F6ITU/K_Driver/Image/Ajax.bmp

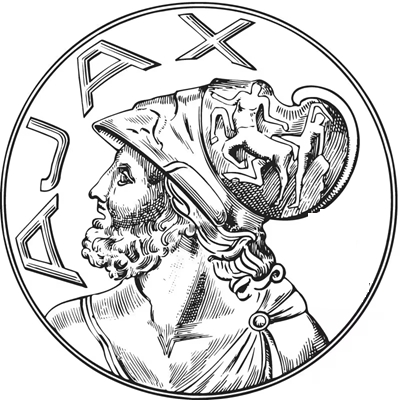
Image/Ajax.bmp
